tbuetow/LED-Christmas-Tree/hw/Base/Light Partition_core_one.3mf

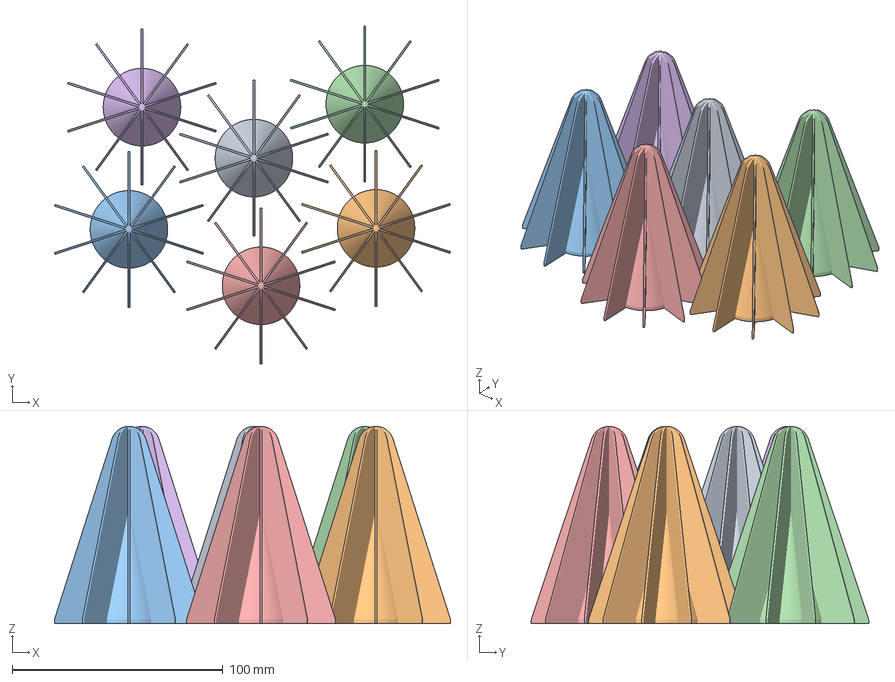
[picture p37: CAD file, 2025-12-13]
hw/Base/Light Partition_core_one.3mf
187.9 x 160.1 x 93.5 mm
