tbuetow/LED-Christmas-Tree/hw/Base/Base_multimaterial_XL.3mf

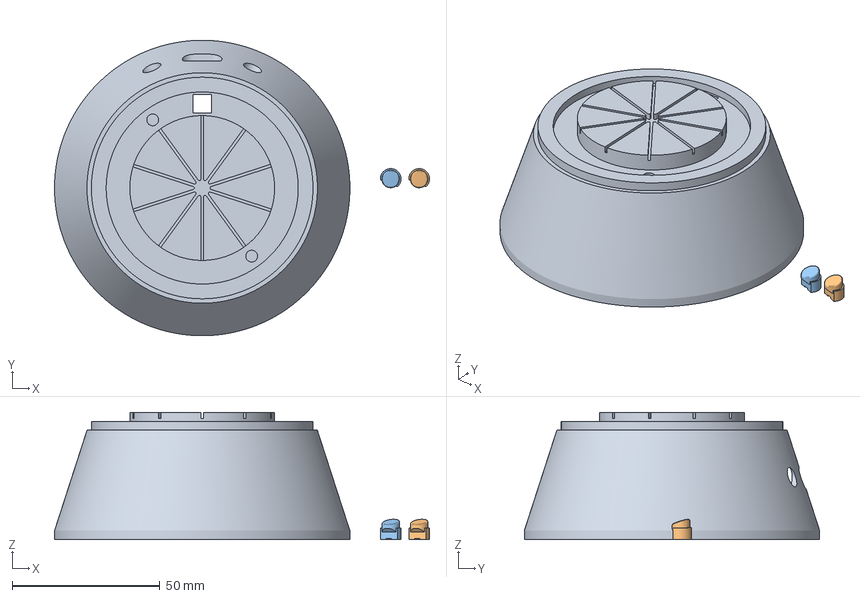
[picture p38: CAD file, 2025-12-07]
hw/Base/Base_multimaterial_XL.3mf
126.9 x 100.0 x 43.0 mm
Base
Button1
Button2
