tbuetow/LED-Christmas-Tree/images/debugging/ATtiny1616 APA102 Timing anomaly 1.jpg

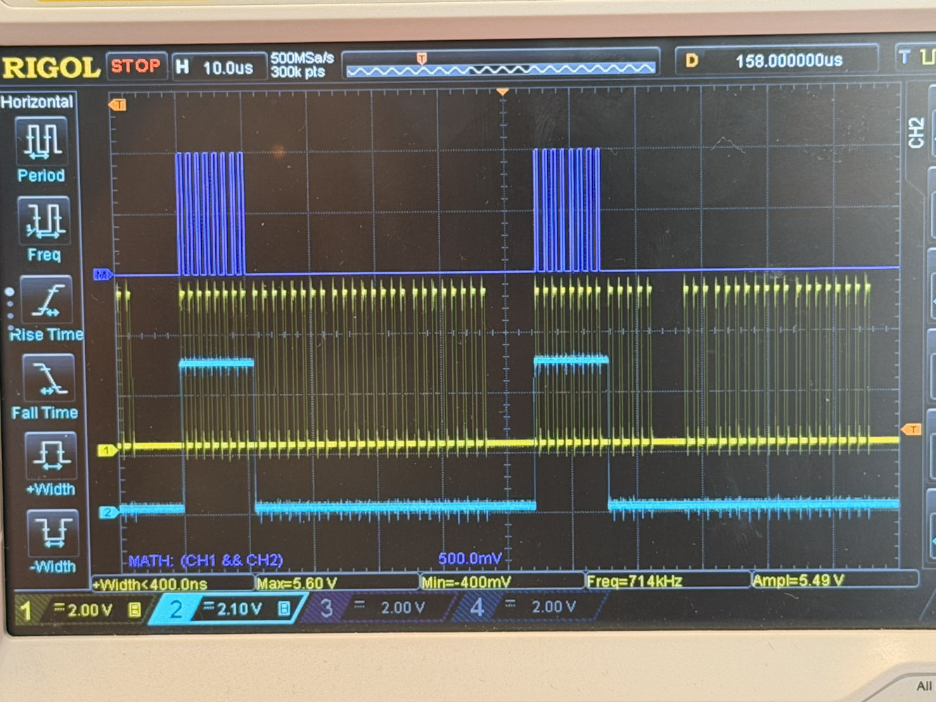
images/debugging/ATtiny1616 APA102 Timing anomaly 1.jpg
